oberlab/jeanCloud/img/jean_process.png

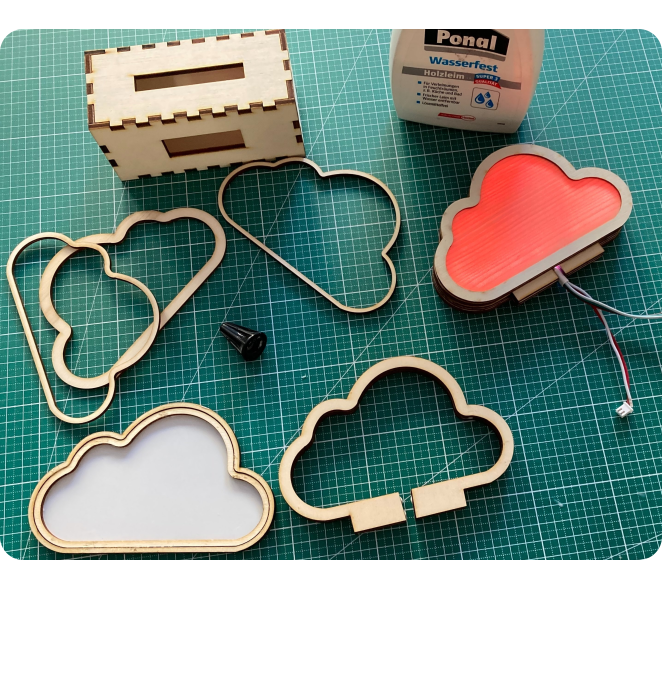
img/jean_process.png
